Qtrocious/Atrocious_Hackpad/pcb/Atrocious_Hackpad.kicad_sch

## KiCad design pcb/Atrocious_Hackpad.kicad_sch (2025-06-11)

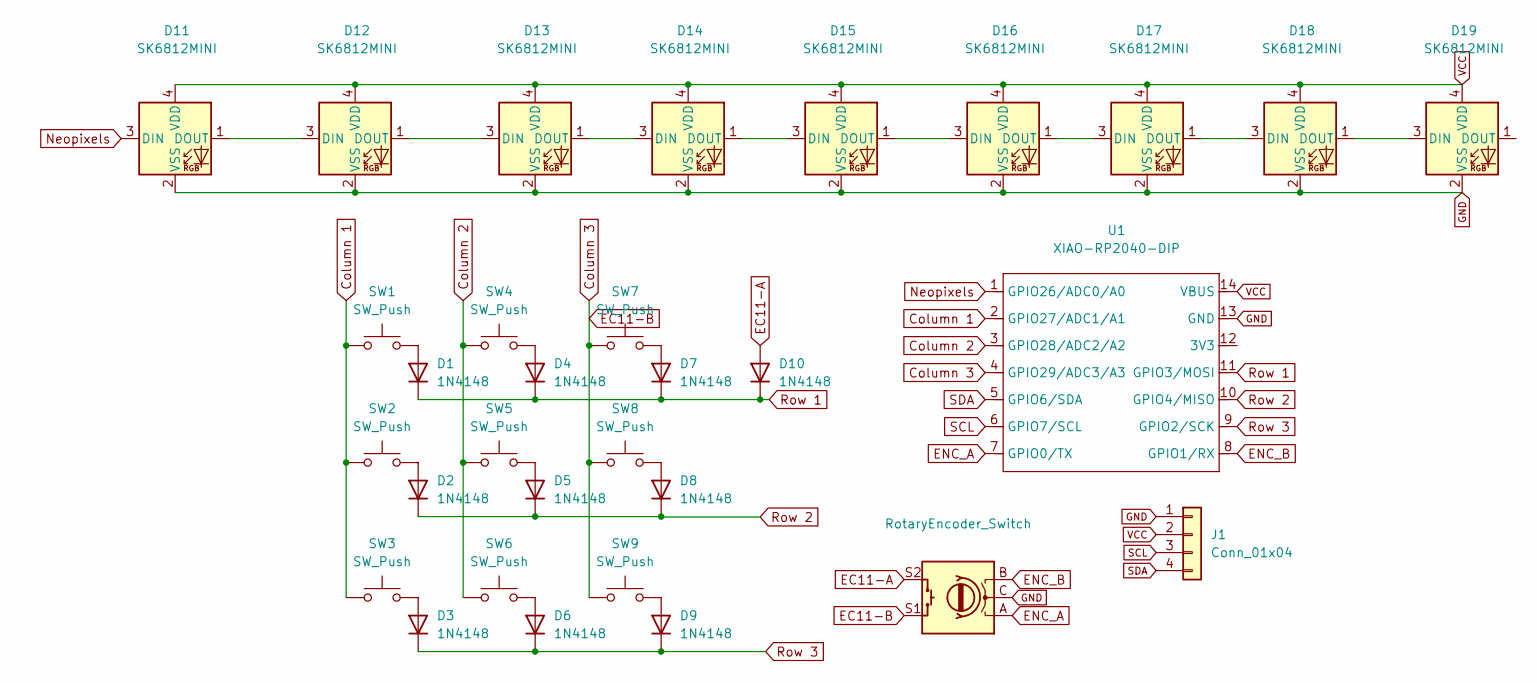
[picture p13: schematic Atrocious_Hackpad.kicad_sch]

Parts:
D1, D2, D3, D4, D5, D6, D7, D8, D9, D10: 1N4148; D_DO-35_SOD27_P7.62mm_Horizontal
D11, D12, D13, D14, D15, D16, D17, D18, D19: SK6812MINI; SK6812-MINI-E
J1: Conn_01x04; OLED_128x32
SW1, SW2, SW3, SW4, SW5, SW6, SW7, SW8, SW9: SW_Push; MX_PCB_1.00u
SW10: RotaryEncoder_Switch; RotaryEncoder_Alps_EC11E-Switch_Vertical_H20mm
U1: XIAO-RP2040-DIP

Connections:
Column 1: SW1.1, SW2.1, SW3.1, U1.2 (GPIO27/ADC1/A1)
Column 2: SW4.1, SW5.1, SW6.1, U1.3 (GPIO28/ADC2/A2)
Column 3: SW7.1, SW8.1, SW9.1, SW10.S1, U1.4 (GPIO29/ADC3/A3)
EC11-A: D10.2 (A), SW10.S2
ENC_A: SW10.A, U1.7 (GPIO0/TX)
ENC_B: SW10.B, U1.8 (GPIO1/RX)
GND: D11.2 (VSS), D12.2 (VSS), D13.2 (VSS), D14.2 (VSS), D15.2 (VSS), D16.2 (VSS), D17.2 (VSS), D18.2 (VSS), D19.2 (VSS), J1.1, SW10.C, U1.13 (GND)
Neopixels: D11.3 (DIN), U1.1 (GPIO26/ADC0/A0)
unnamed: D1.2 (A), SW1.2
unnamed: D2.2 (A), SW2.2
unnamed: D3.2 (A), SW3.2
unnamed: D4.2 (A), SW4.2
unnamed: D5.2 (A), SW5.2
unnamed: D6.2 (A), SW6.2
unnamed: D7.2 (A), SW7.2
unnamed: D8.2 (A), SW8.2
unnamed: D9.2 (A), SW9.2
unnamed: D11.1 (DOUT), D12.3 (DIN)
unnamed: D12.1 (DOUT), D13.3 (DIN)
unnamed: D13.1 (DOUT), D14.3 (DIN)
unnamed: D14.1 (DOUT), D15.3 (DIN)
unnamed: D15.1 (DOUT), D16.3 (DIN)
unnamed: D16.1 (DOUT), D17.3 (DIN)
unnamed: D17.1 (DOUT), D18.3 (DIN)
unnamed: D18.1 (DOUT), D19.3 (DIN)
Row 1: D1.1 (K), D4.1 (K), D7.1 (K), D10.1 (K), U1.11 (GPIO3/MOSI)
Row 2: D2.1 (K), D5.1 (K), D8.1 (K), U1.10 (GPIO4/MISO)
Row 3: D3.1 (K), D6.1 (K), D9.1 (K), U1.9 (GPIO2/SCK)
SCL: J1.3, U1.6 (GPIO7/SCL)
SDA: J1.4, U1.5 (GPIO6/SDA)
VCC: D11.4 (VDD), D12.4 (VDD), D13.4 (VDD), D14.4 (VDD), D15.4 (VDD), D16.4 (VDD), D17.4 (VDD), D18.4 (VDD), D19.4 (VDD), J1.2, U1.14 (VBUS)
